taunoe/pi-pico-andur/datasheets/Mini360-2d-model.jpg

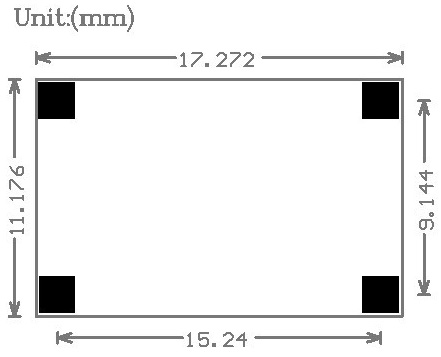
datasheets/Mini360-2d-model.jpg
