taunoe/pi-pico-andur/distance.jpg

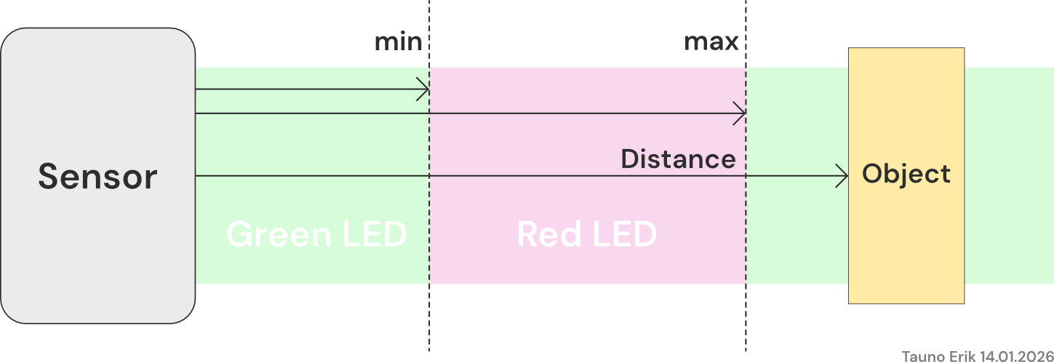
distance.jpg
