taunoe/pi-pico-andur/img/pocitive_polarity.png

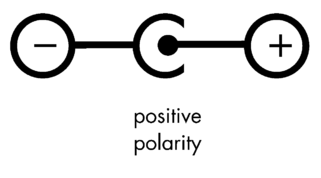
img/pocitive_polarity.png
