taunoe/pi-pico-andur/KiCad/pcb/pcb.png

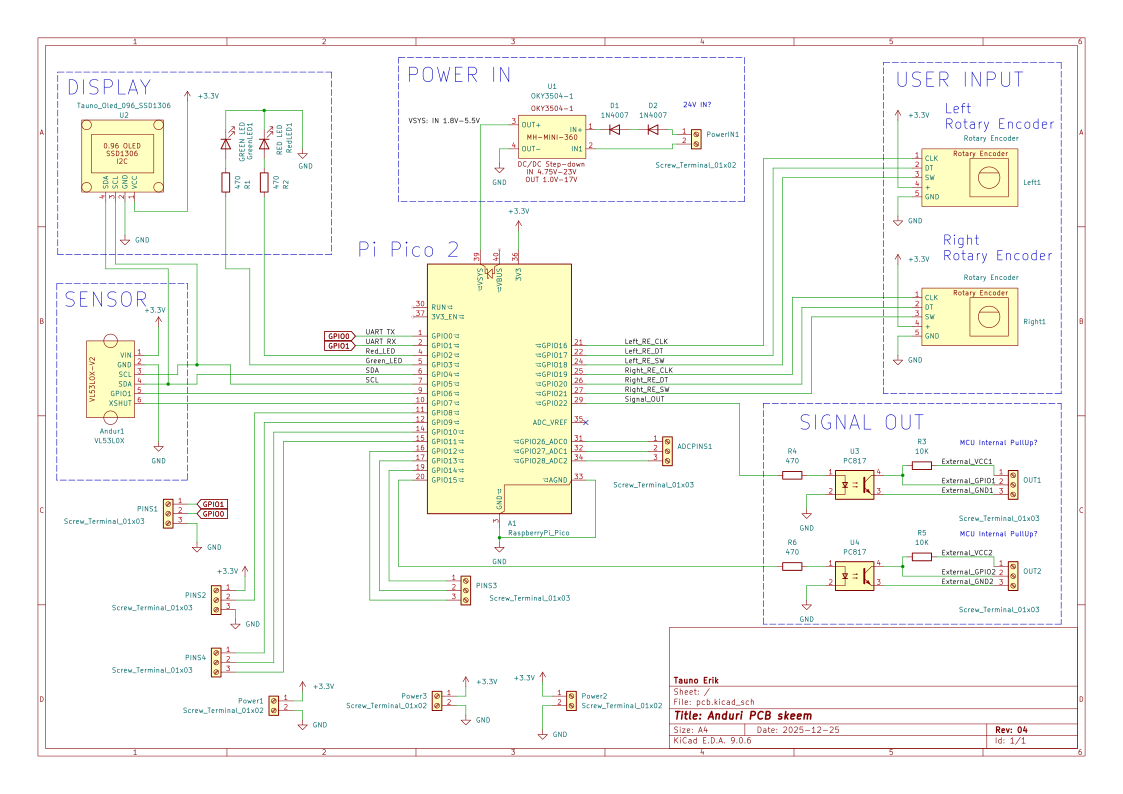
KiCad/pcb/pcb.png
