taunoe/pi-pico-andur/3d_models/Rotary-Encoder.step

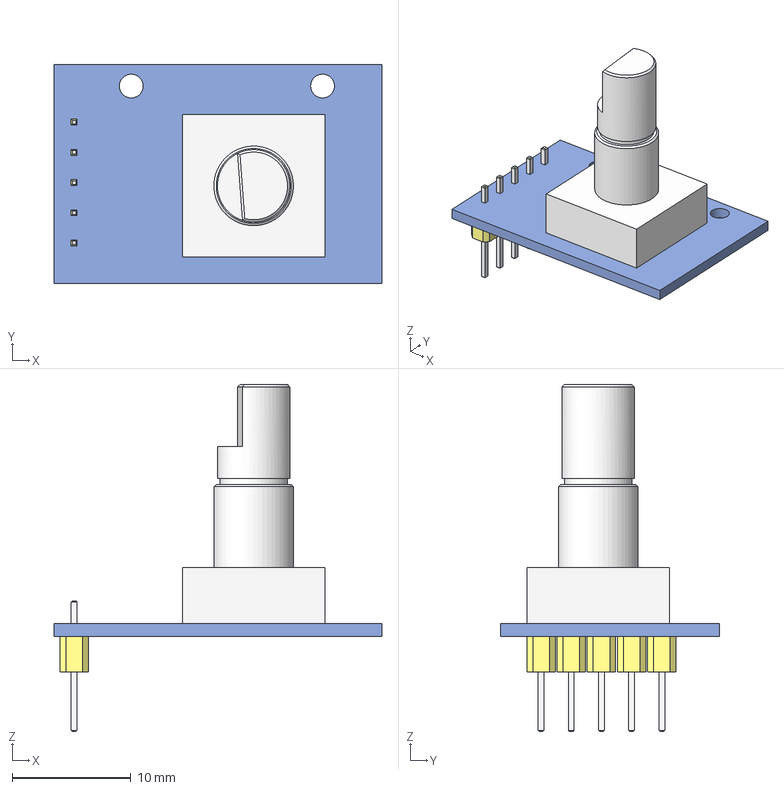
[picture p46: CAD file, 2025-11-19]
3d_models/Rotary-Encoder.step
27.6 x 18.4 x 29.2 mm
