taunoe/pi-pico-andur/3d_models/v2/v2_ülemine_raam.SLDPRT

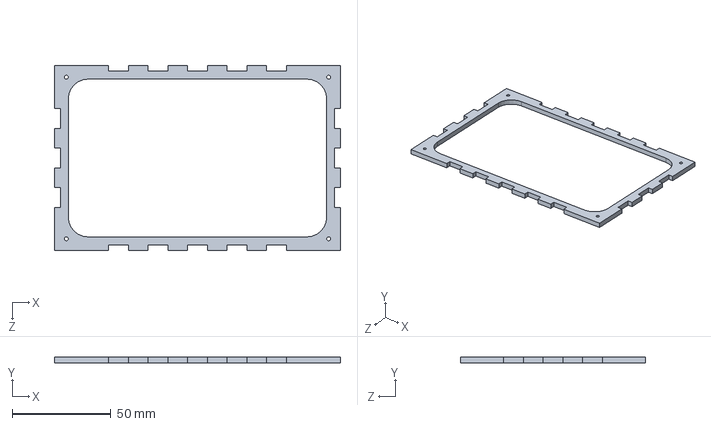
[picture p47: CAD file, 2026-01-14]
3d_models/v2/v2_ülemine_raam.SLDPRT
145.0 x 3.00 x 94.0 mm
