taunoe/pi-pico-andur/3d_models/v2_3.8mm/anduri_karp/v2_andur_tof.SLDPRT

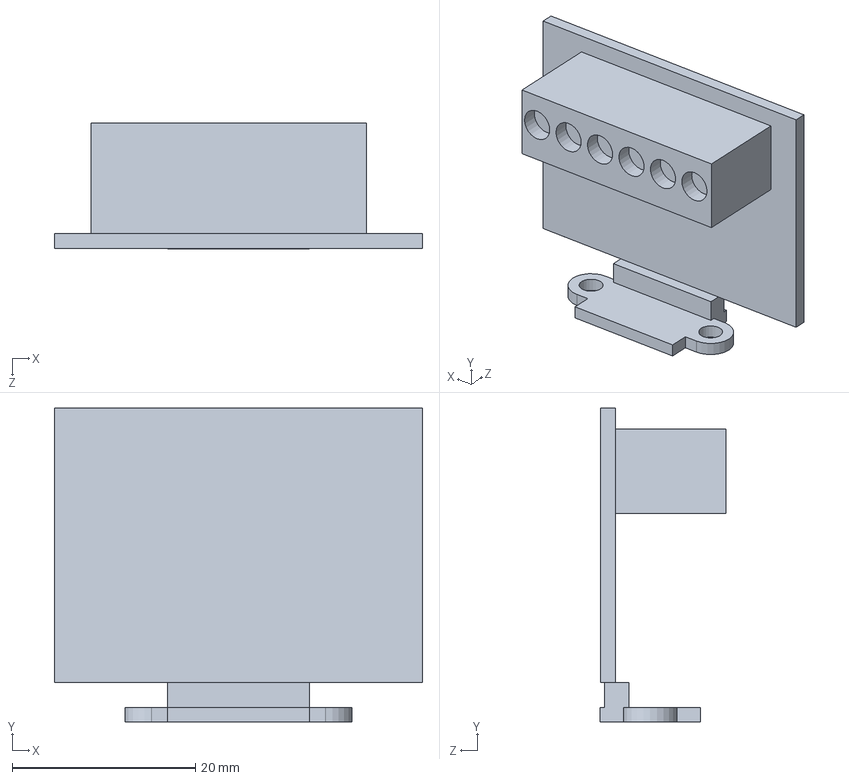
[picture p48: CAD file, 2026-01-20]
3d_models/v2_3.8mm/anduri_karp/v2_andur_tof.SLDPRT
40.2 x 34.3 x 13.8 mm
