taunoe/pi-pico-andur/3d_models/v2_3.8mm/v2_põhi.SLDPRT

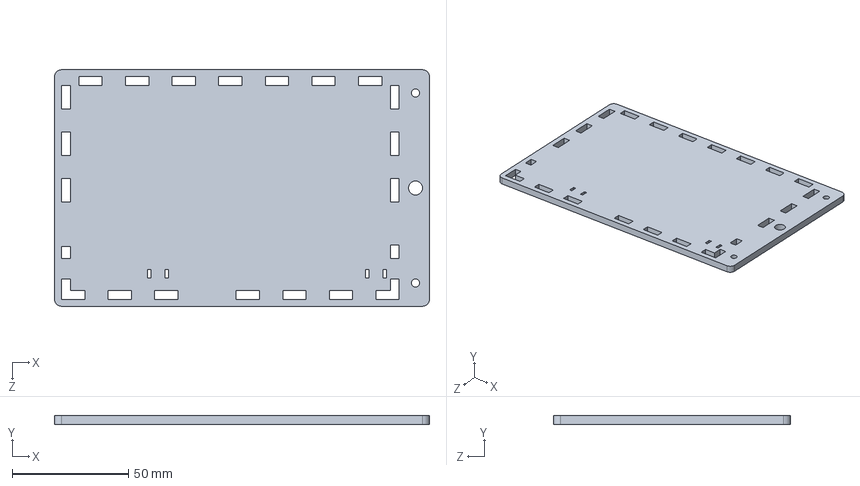
[picture p49: CAD file, 2026-01-20]
3d_models/v2_3.8mm/v2_põhi.SLDPRT
161.0 x 3.80 x 101.6 mm
