taunoe/pi-pico-andur/3d_models/v2/v2_põhi.SLDPRT

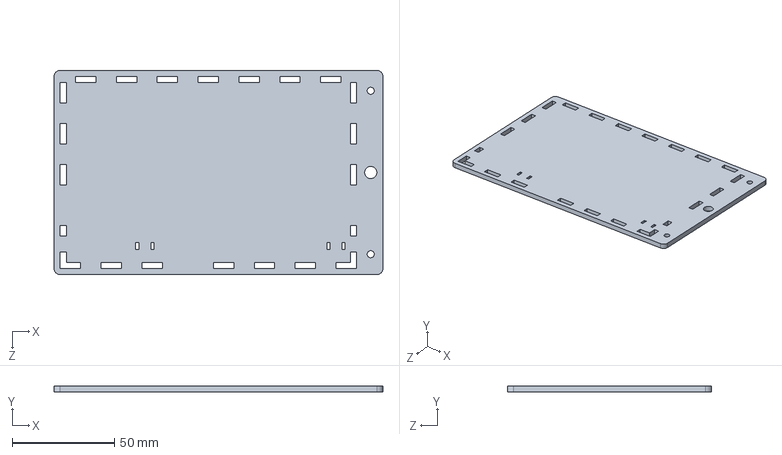
[picture p50: CAD file, 2026-01-14]
3d_models/v2/v2_põhi.SLDPRT
161.0 x 3.00 x 100.0 mm
