taunoe/pi-pico-andur/3d_models/v2_3.8mm/anduri_karp/v2_andur_kaane_juhtmeauk.SLDPRT

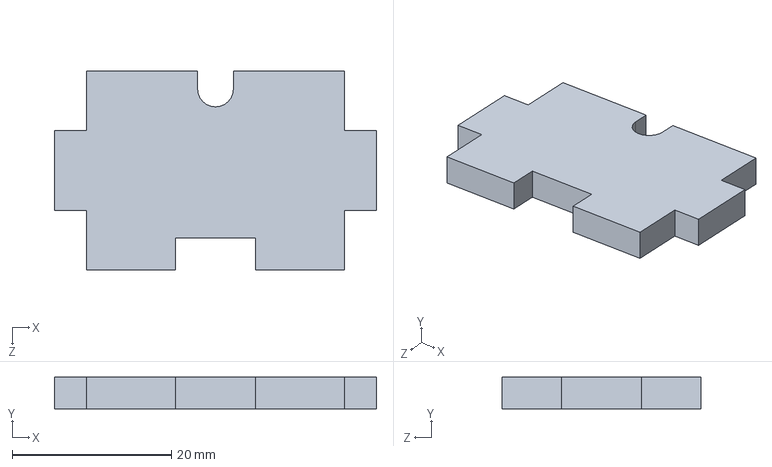
[picture p51: CAD file, 2026-01-20]
3d_models/v2_3.8mm/anduri_karp/v2_andur_kaane_juhtmeauk.SLDPRT
40.5 x 4.00 x 25.0 mm
