taunoe/pi-pico-andur/3d_models/v2_3.8mm/v2_alusraam.SLDPRT

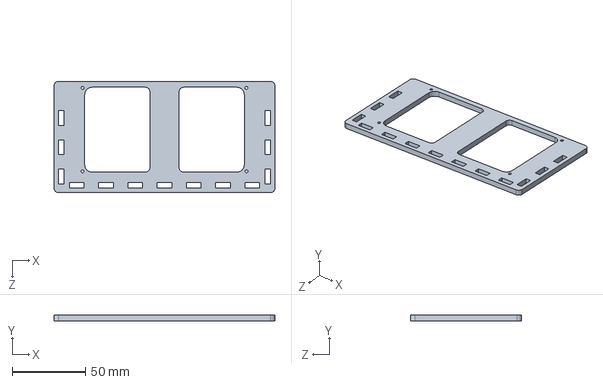
[picture p52: CAD file, 2026-01-20]
3d_models/v2_3.8mm/v2_alusraam.SLDPRT
151.0 x 3.80 x 76.0 mm
