taunoe/pi-pico-andur/3d_models/v2/v2_külg_pikem.SLDPRT

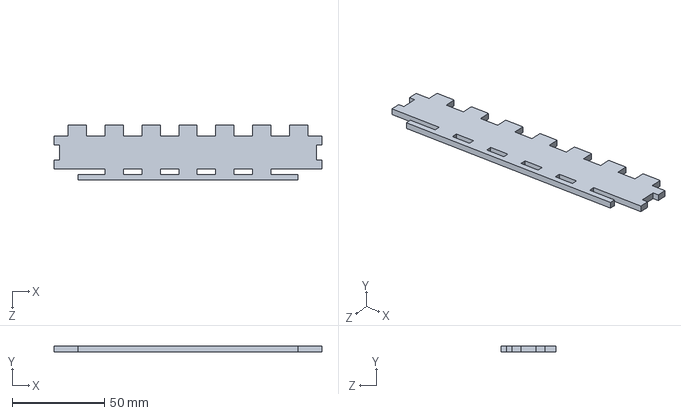
[picture p53: CAD file, 2026-01-14]
3d_models/v2/v2_külg_pikem.SLDPRT
145.0 x 3.00 x 30.0 mm
