taunoe/pi-pico-andur/3d_models/v2_3.8mm/v2_ülemine_raam.SLDPRT

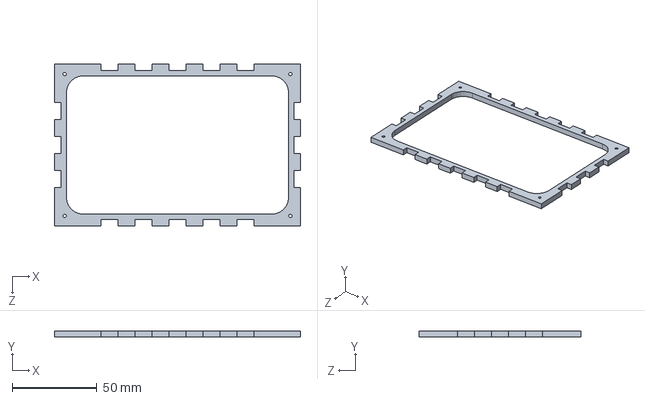
[picture p55: CAD file, 2026-01-20]
3d_models/v2_3.8mm/v2_ülemine_raam.SLDPRT
145.0 x 3.80 x 95.6 mm
