taunoe/pi-pico-andur/3d_models/v2_3.8mm/anduri_karp/v2_andur_kaane_lagi.SLDPRT

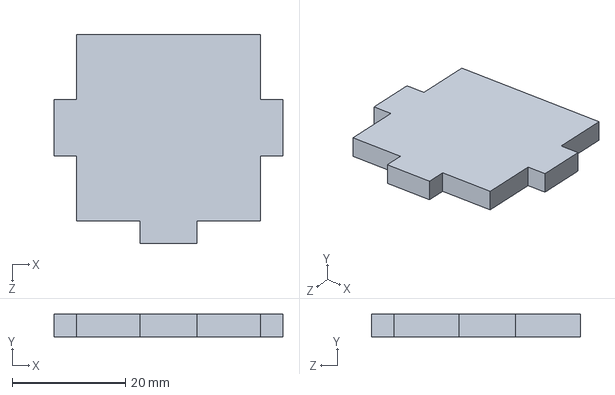
[picture p56: CAD file, 2026-01-20]
3d_models/v2_3.8mm/anduri_karp/v2_andur_kaane_lagi.SLDPRT
40.5 x 4.00 x 37.0 mm
