taunoe/pi-pico-andur/3d_models/v2_3.8mm/v2_külg_lühem.SLDPRT

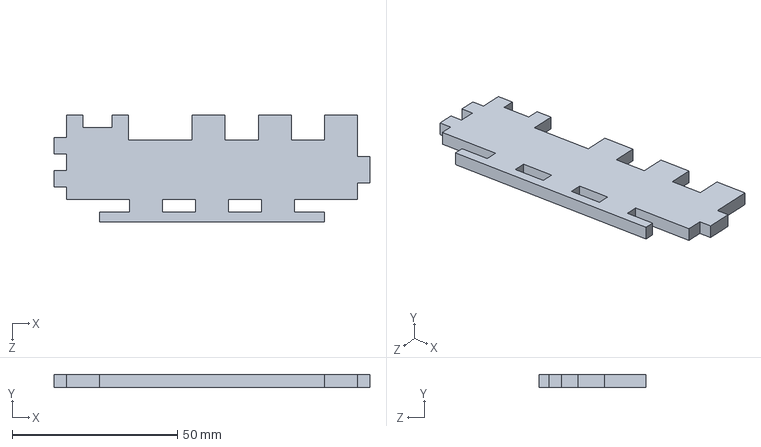
[picture p57: CAD file, 2026-01-20]
3d_models/v2_3.8mm/v2_külg_lühem.SLDPRT
95.6 x 3.80 x 32.4 mm
