taunoe/pi-pico-andur/3d_models/v2_3.8mm/anduri_karp/v2_andur_esi_6MM.DXF

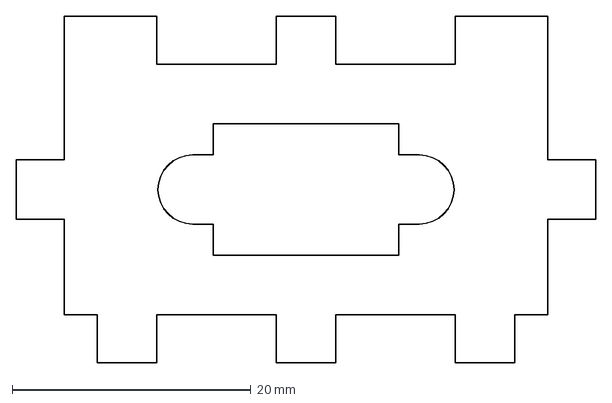
[picture p59: CAD file, 2026-01-20]
3d_models/v2_3.8mm/anduri_karp/v2_andur_esi_6MM.DXF
48.5 x 29.0 mm
