taunoe/pi-pico-andur/3d_models/v2_3.8mm/v2_külg_pikem_avadega.SLDPRT

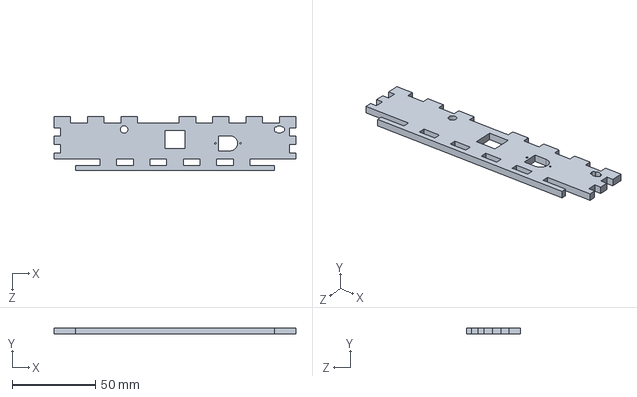
[picture p60: CAD file, 2026-01-20]
3d_models/v2_3.8mm/v2_külg_pikem_avadega.SLDPRT
145.0 x 3.80 x 32.4 mm
