taunoe/pi-pico-andur/3d_models/v2/v2_alusraam.SLDPRT

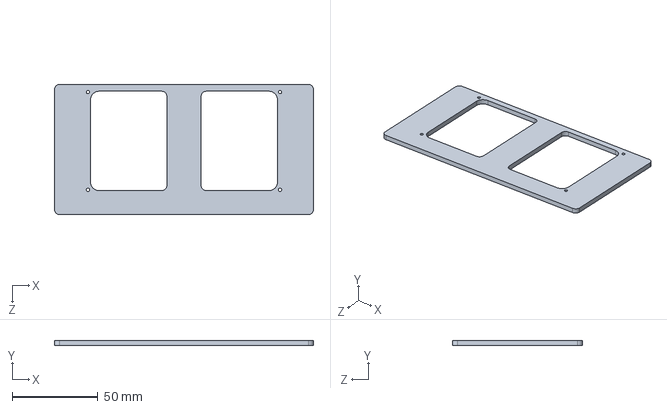
[picture p61: CAD file, 2026-01-08]
3d_models/v2/v2_alusraam.SLDPRT
151.0 x 3.00 x 76.0 mm
