taunoe/pi-pico-andur/3d_models/v2_3.8mm/anduri_karp/v2_andur_külg.SLDPRT

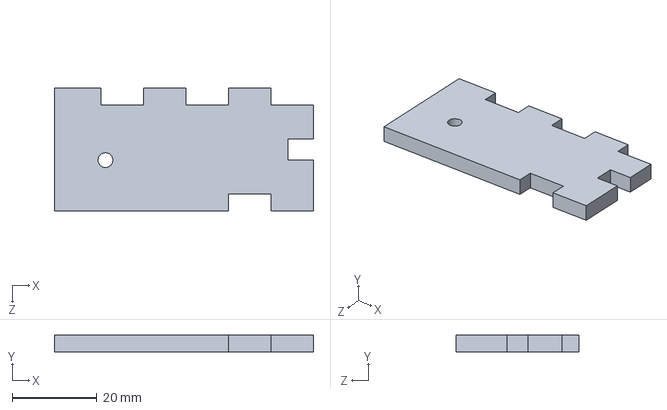
[picture p62: CAD file, 2026-01-20]
3d_models/v2_3.8mm/anduri_karp/v2_andur_külg.SLDPRT
61.0 x 4.00 x 29.0 mm
