taunoe/pi-pico-andur/3d_models/v2_3.8mm/v2_külg_pikem.SLDPRT

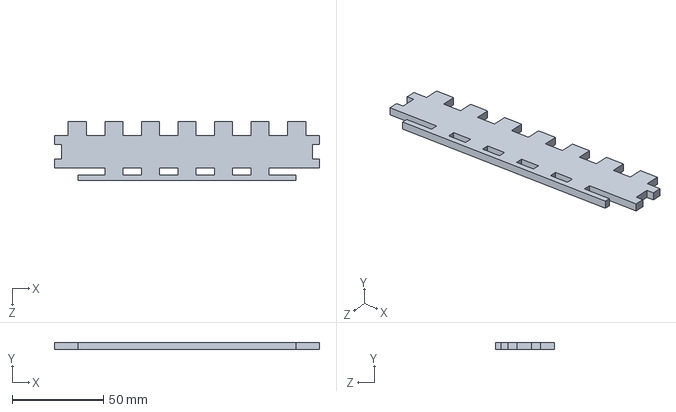
[picture p63: CAD file, 2026-01-20]
3d_models/v2_3.8mm/v2_külg_pikem.SLDPRT
145.0 x 3.80 x 32.4 mm
