taunoe/pi-pico-andur/3d_models/v2_3.8mm/anduri_karp/v2_andur_pealmine.SLDPRT

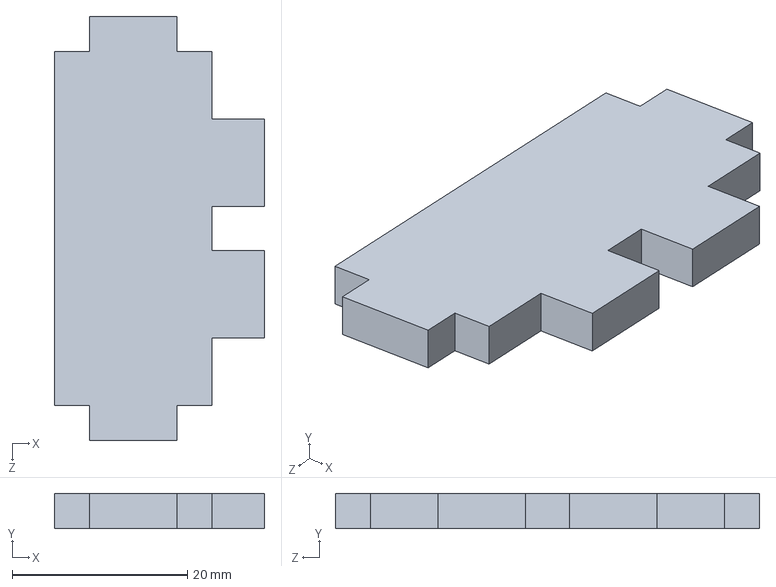
[picture p64: CAD file, 2026-01-20]
3d_models/v2_3.8mm/anduri_karp/v2_andur_pealmine.SLDPRT
24.0 x 4.00 x 48.5 mm
