taunoe/pi-pico-andur/3d_models/v2_3.8mm/v2_power_raam.SLDPRT

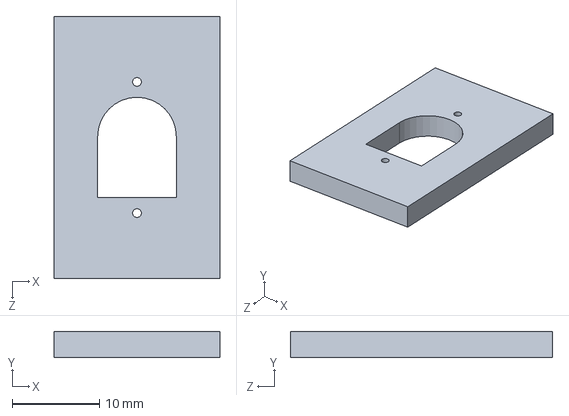
[picture p65: CAD file, 2026-01-14]
3d_models/v2_3.8mm/v2_power_raam.SLDPRT
19.0 x 3.00 x 30.0 mm
